nickarad/iot-ecg-nodemcu/arduino/secret-config.example.h

// Update these with values suitable for your network.
const char* ssid = "your_ssid";
const char* password = "your_password";
const char* mqtt_server = "192.168.0.121"; 
const char* mqtt_user = "admin";
const char* mqtt_pass= "admin";
